Sergio55Veliz/Ortesis-mano/Pictures/Piezas impresas/1 Hand ring.png

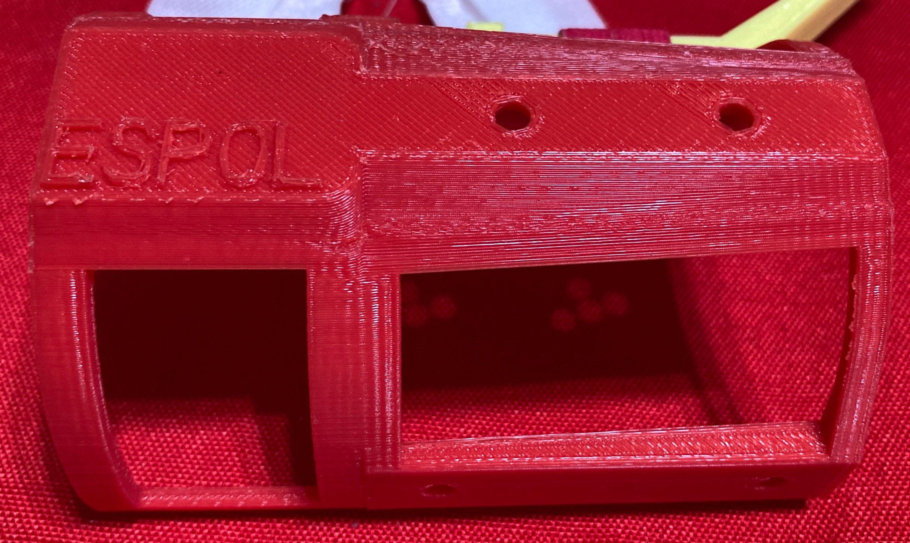
Pictures/Piezas impresas/1 Hand ring.png
