Sergio55Veliz/Ortesis-mano/Pictures/Piezas impresas/2 Hand Stag Straight.png

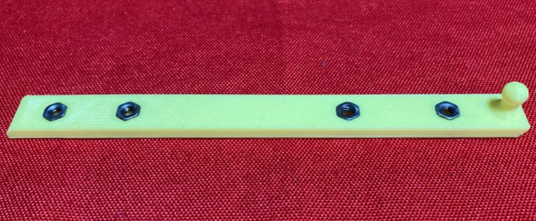
Pictures/Piezas impresas/2 Hand Stag Straight.png
