Sergio55Veliz/Ortesis-mano/Pictures/Piezas impresas/3 Thumb Stag.png

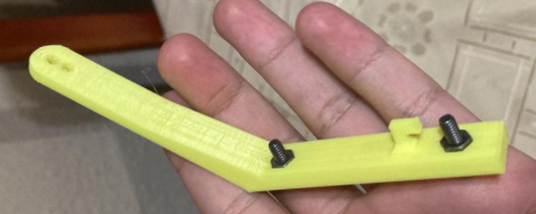
Pictures/Piezas impresas/3 Thumb Stag.png
