Sergio55Veliz/Ortesis-mano/Pictures/Piezas impresas/4 Overhand.png

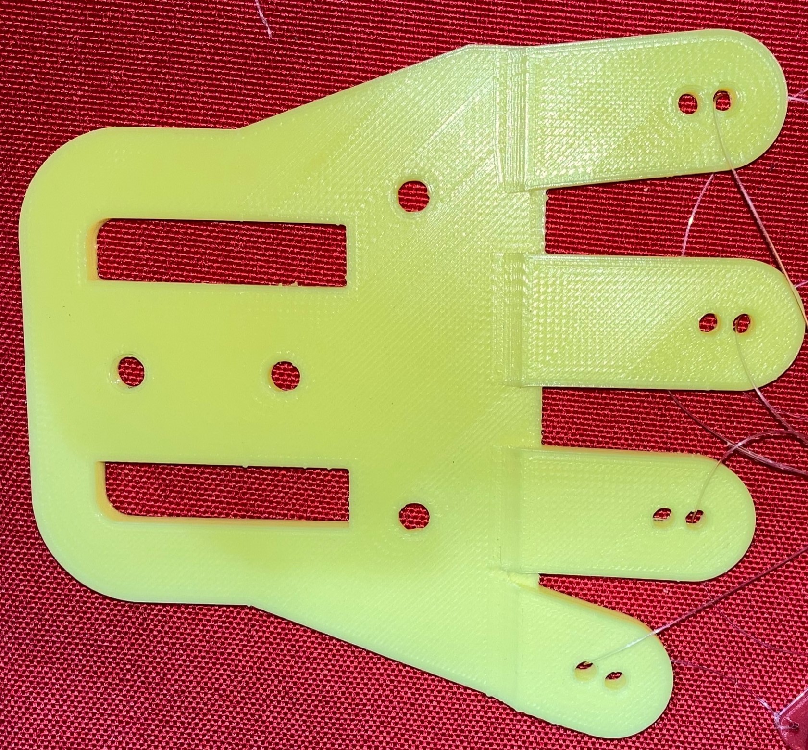
Pictures/Piezas impresas/4 Overhand.png
