Sergio55Veliz/Ortesis-mano/Pictures/Piezas impresas/5 Fingers.png

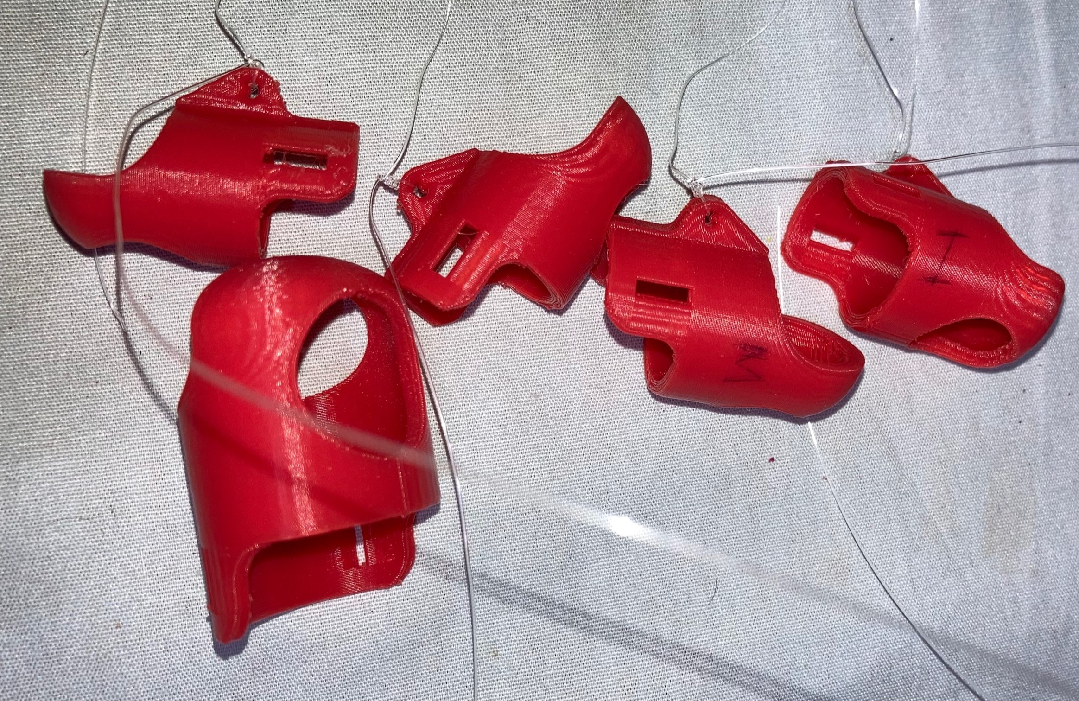
Pictures/Piezas impresas/5 Fingers.png
