Sergio55Veliz/Ortesis-mano/Pictures/Piezas impresas/6 Knut (top y botton).png

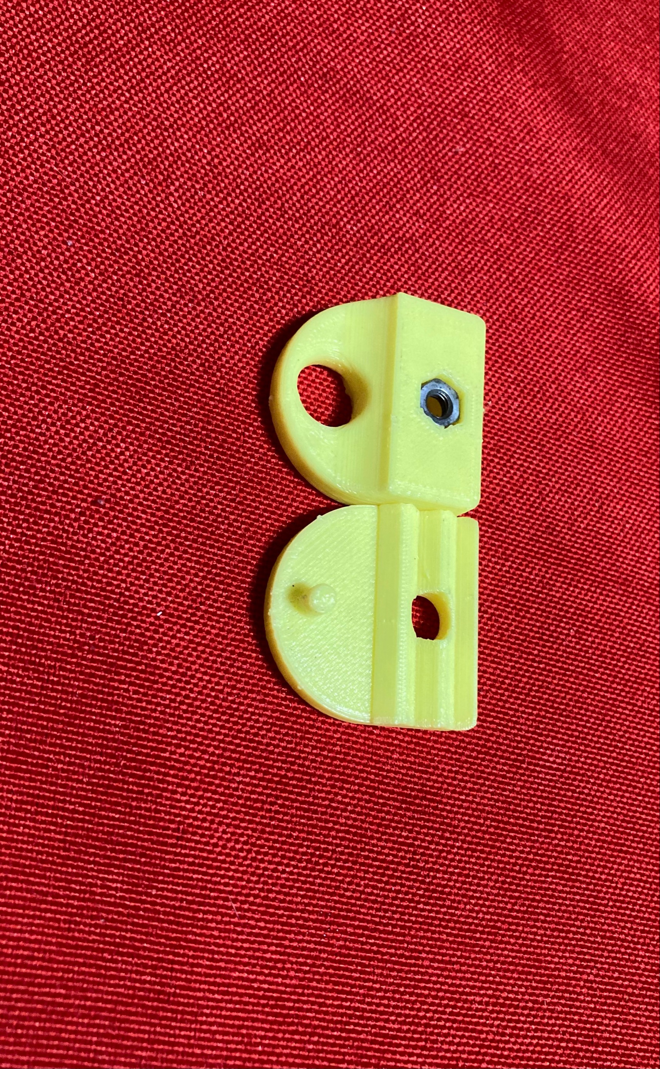
Pictures/Piezas impresas/6 Knut (top y botton).png
