Sergio55Veliz/Ortesis-mano/Pictures/Ensamble/2.png

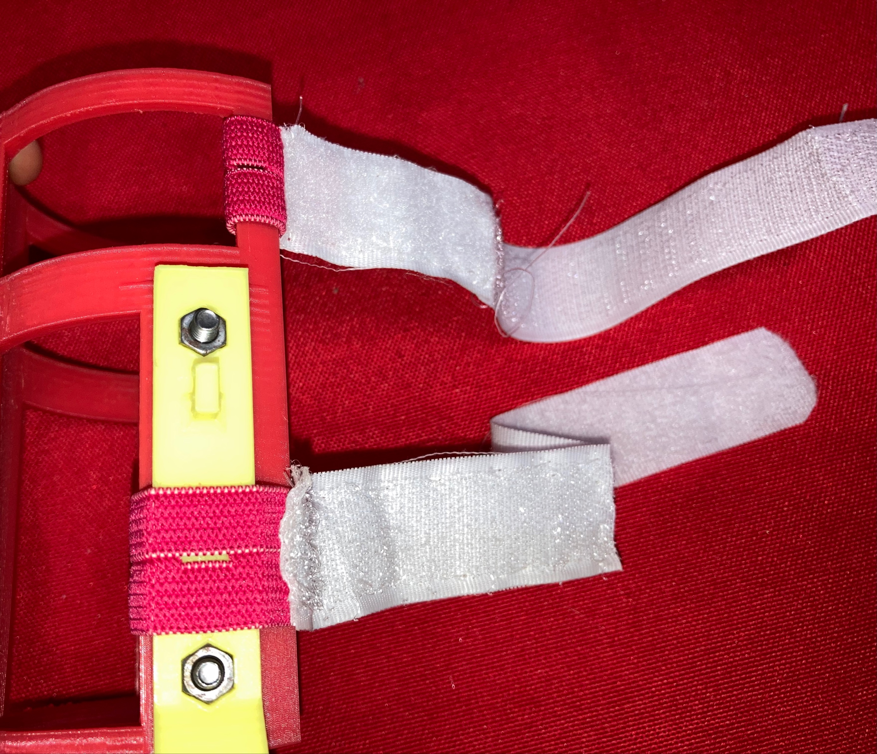
Pictures/Ensamble/2.png
