Sergio55Veliz/Ortesis-mano/Pictures/Ensamble/3.png

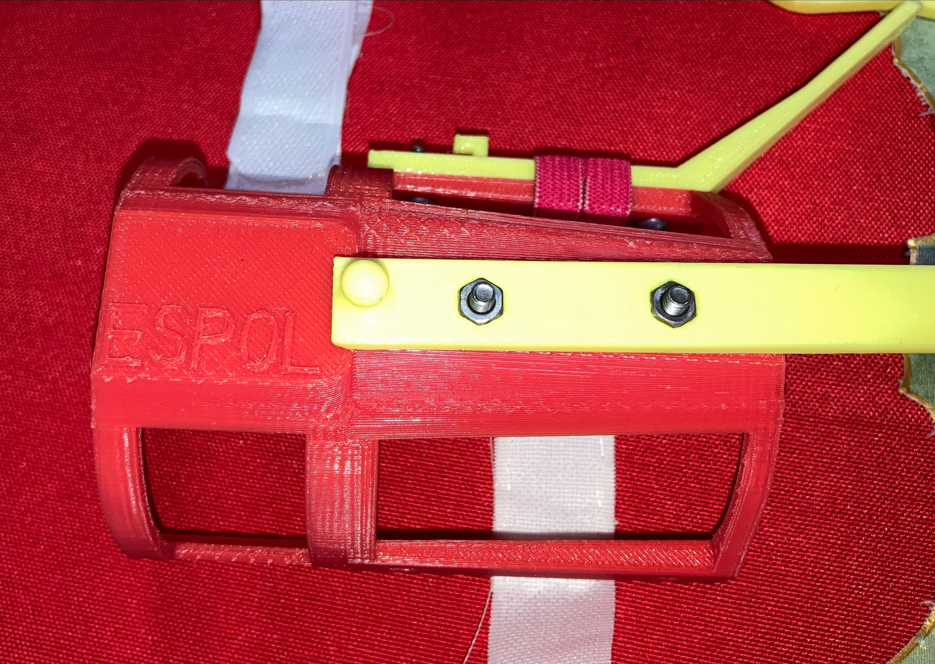
Pictures/Ensamble/3.png
