Sergio55Veliz/Ortesis-mano/Pictures/Ensamble/4.png

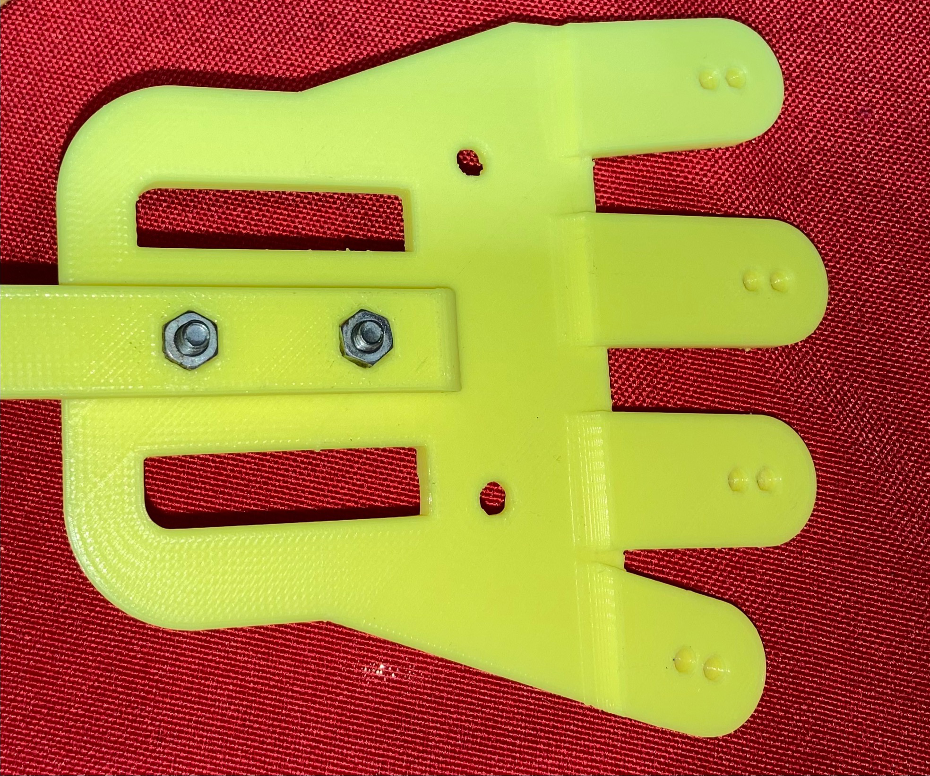
Pictures/Ensamble/4.png
