Sergio55Veliz/Ortesis-mano/Pictures/Ensamble/6.png

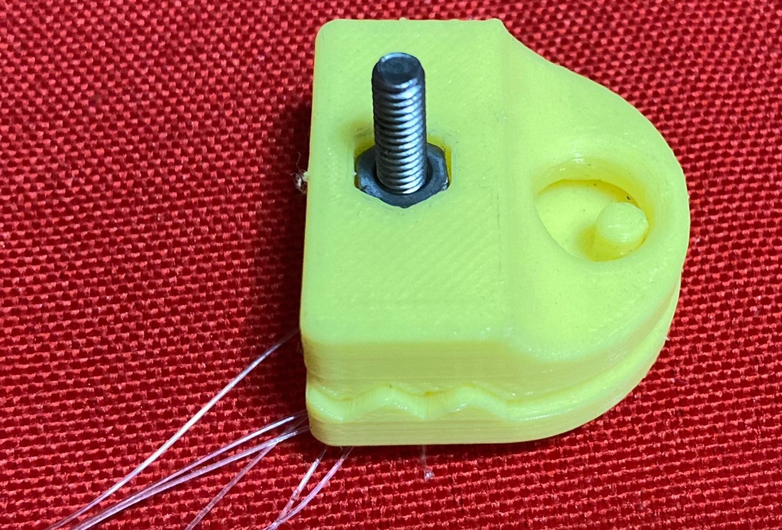
Pictures/Ensamble/6.png
