Sergio55Veliz/Ortesis-mano/Pictures/Ensamble/8.png

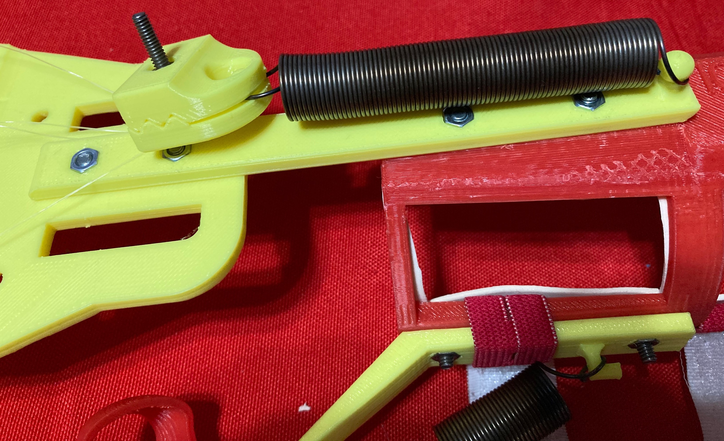
Pictures/Ensamble/8.png
