Sergio55Veliz/Ortesis-mano/Pictures/Ensamble/9.png

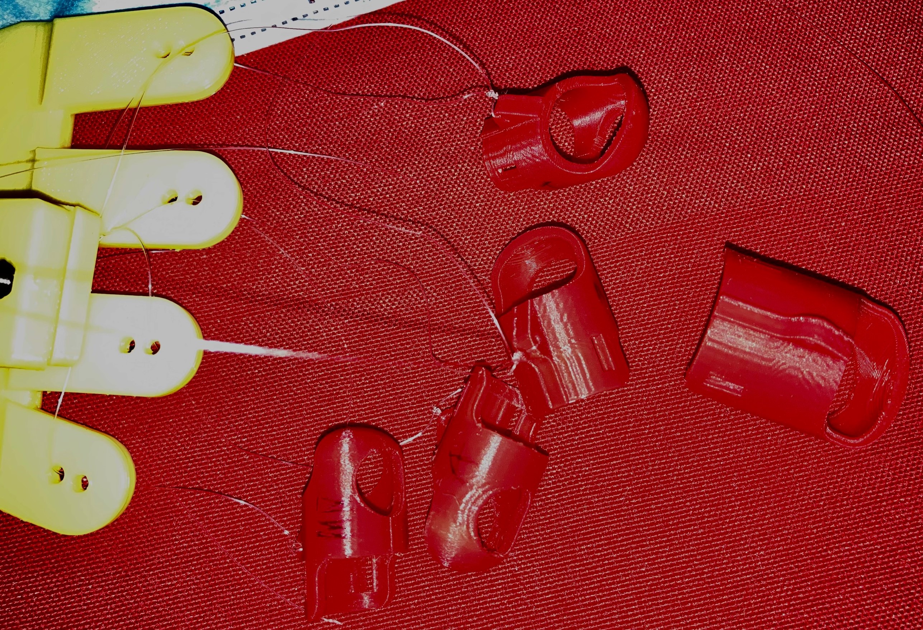
Pictures/Ensamble/9.png
