Sergio55Veliz/Ortesis-mano/Pictures/Ensamble/Vista inferior.png

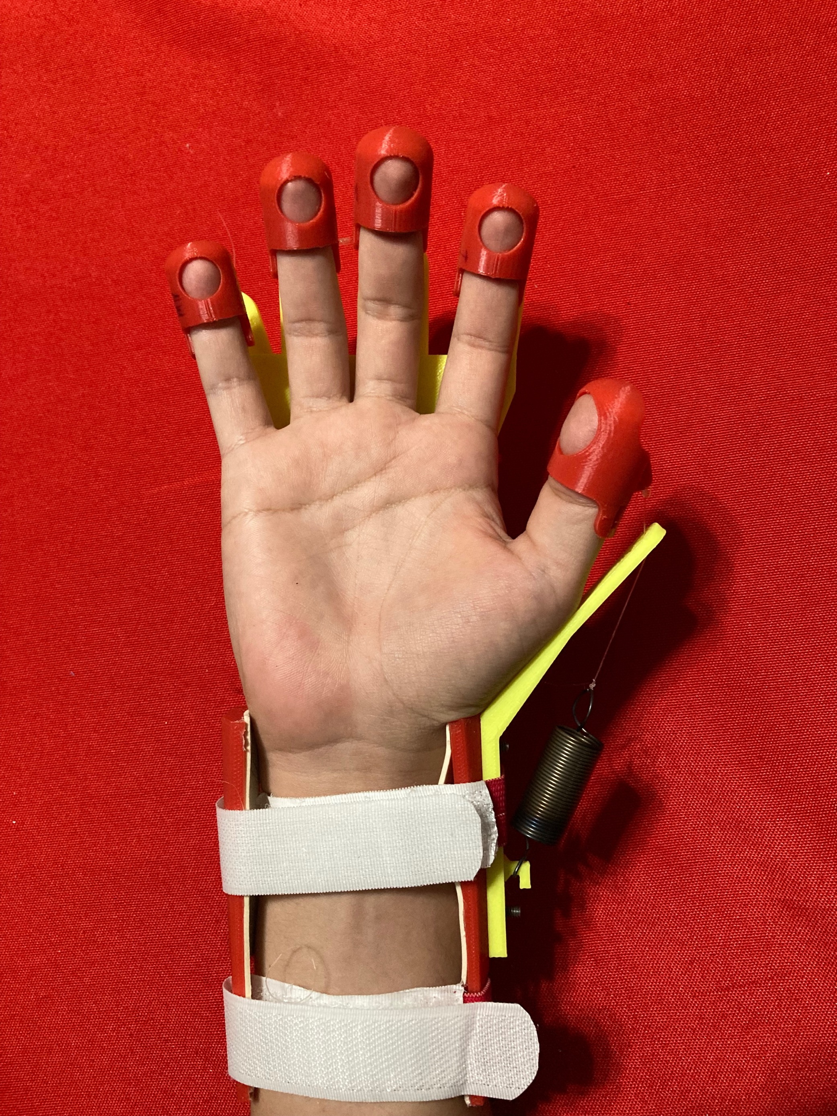
Pictures/Ensamble/Vista inferior.png
