Sergio55Veliz/Ortesis-mano/Pictures/Ensamble/Vista lateral - flexionado.png

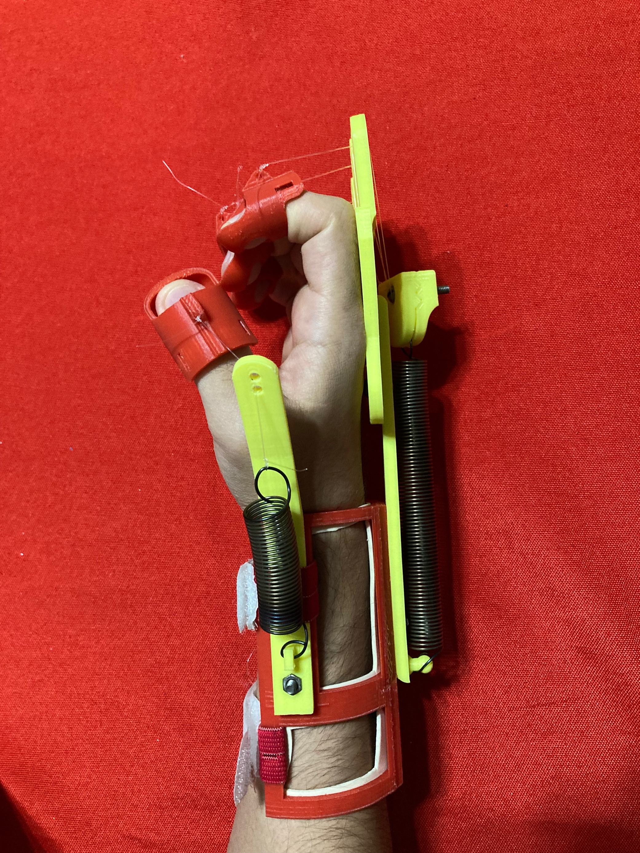
Pictures/Ensamble/Vista lateral - flexionado.png
