Sergio55Veliz/Ortesis-mano/Pictures/Ensamble/Vista superior.png

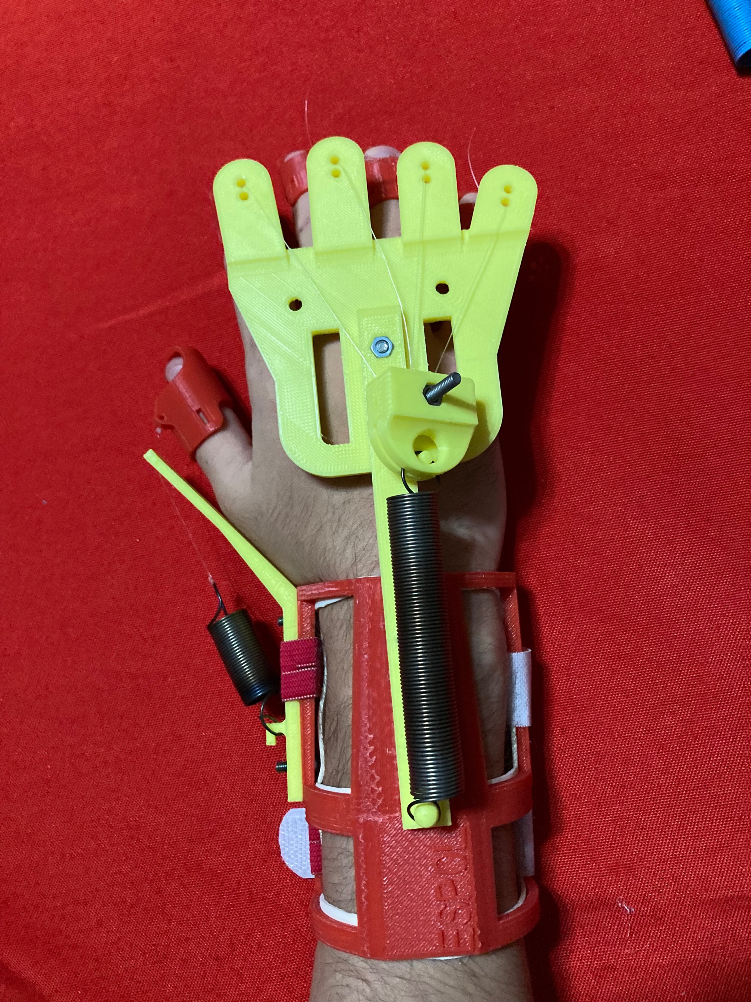
Pictures/Ensamble/Vista superior.png
